nslogan/RJ45-LED-Breakout/release/1.0/Photos/RJ45-LED-v1.0-2pop-1upop-02.jpg

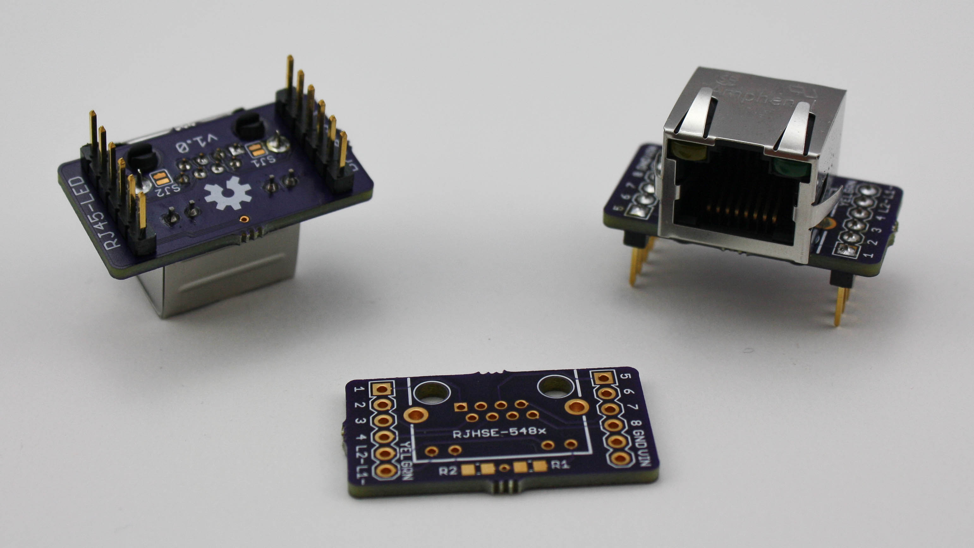
release/1.0/Photos/RJ45-LED-v1.0-2pop-1upop-02.jpg
