nslogan/RJ45-LED-Breakout/release/1.0/Photos/RJ45-LED-v1.0-top.jpg

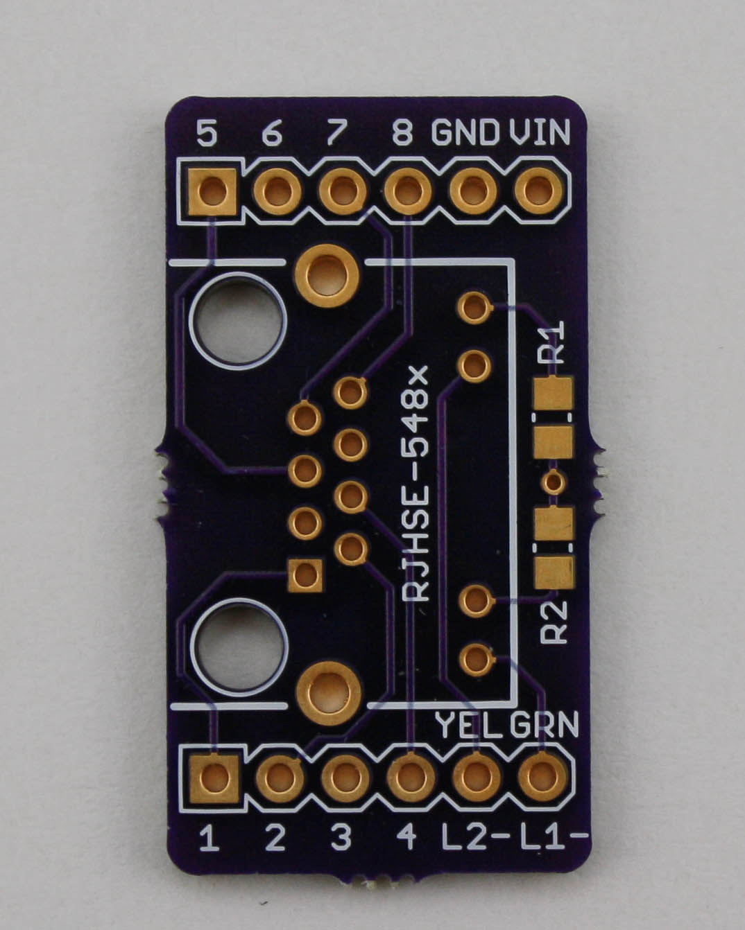
release/1.0/Photos/RJ45-LED-v1.0-top.jpg
