nslogan/RJ45-LED-Breakout/release/1.0/RJ45-LED-Breakout_board-top_1.0.png

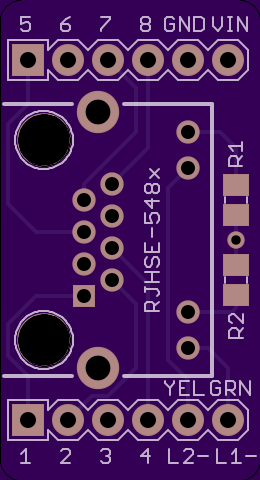
release/1.0/RJ45-LED-Breakout_board-top_1.0.png
